ssbb/PseudoMakeMeKeyCapProfiles/stl/single_keys/cs_r2_lateral_r.stl

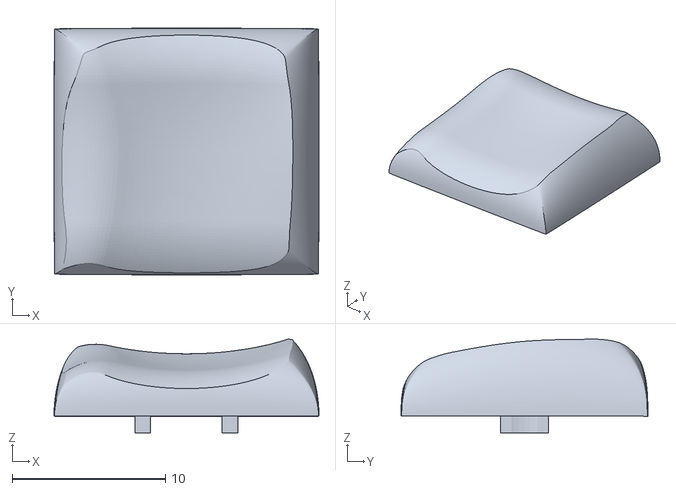
[picture p18: CAD file, 2023-09-04]
stl/single_keys/cs_r2_lateral_r.stl
17.3 x 16.1 x 6.12
