ssbb/PseudoMakeMeKeyCapProfiles/stl/single_keys/cs_r3_2.stl

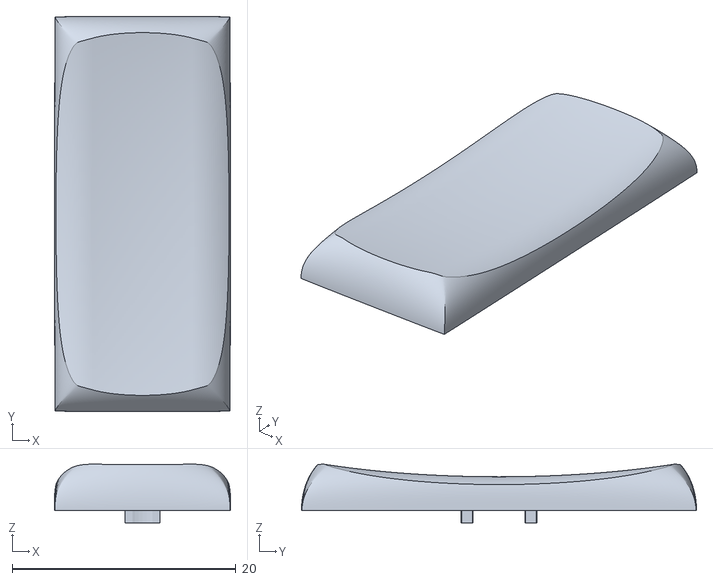
[picture p19: CAD file, 2023-09-04]
stl/single_keys/cs_r3_2.stl
15.7 x 35.3 x 5.24
