ssbb/PseudoMakeMeKeyCapProfiles/stl/single_keys/cs_r3_175.stl

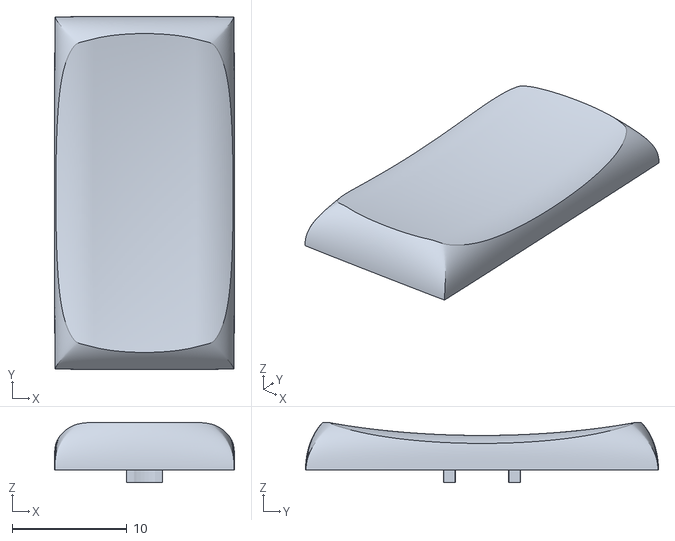
[picture p20: CAD file, 2023-09-04]
stl/single_keys/cs_r3_175.stl
15.7 x 30.8 x 5.25
