ssbb/PseudoMakeMeKeyCapProfiles/stl/single_keys/cs_r4x_1.stl

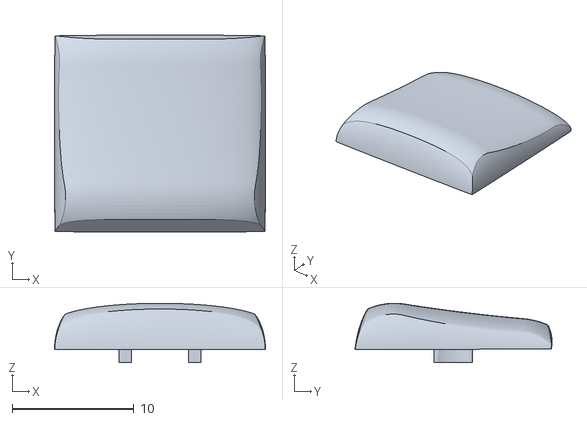
[picture p21: CAD file, 2023-09-04]
stl/single_keys/cs_r4x_1.stl
17.3 x 16.2 x 4.88
