ssbb/PseudoMakeMeKeyCapProfiles/stl/single_keys/cs_r3_125_bar.stl

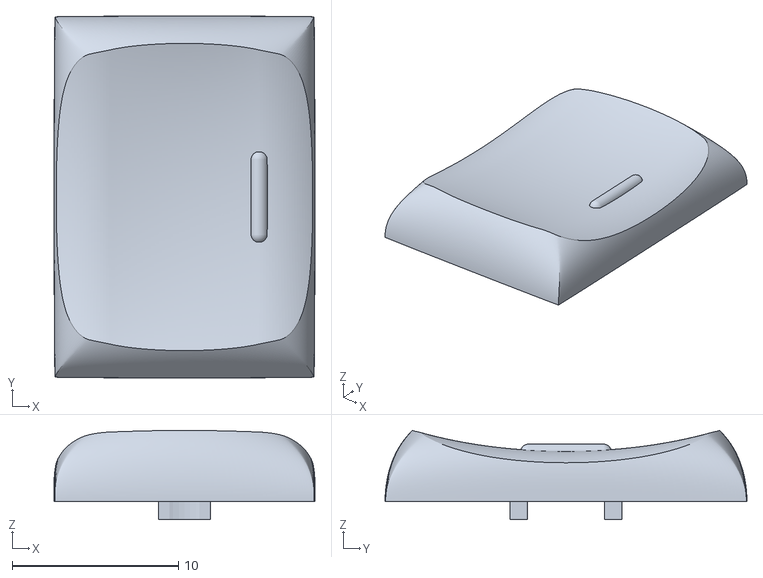
[picture p22: CAD file, 2023-09-04]
stl/single_keys/cs_r3_125_bar.stl
15.7 x 21.8 x 5.37
