ssbb/PseudoMakeMeKeyCapProfiles/stl/single_keys/cs_r3_225.stl

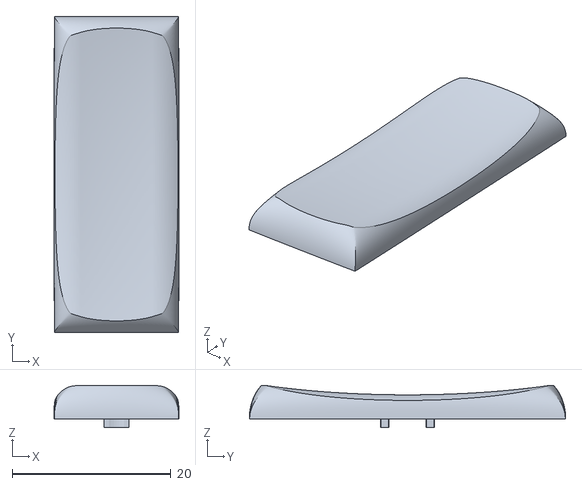
[picture p23: CAD file, 2023-09-04]
stl/single_keys/cs_r3_225.stl
15.7 x 39.8 x 5.30
