ssbb/PseudoMakeMeKeyCapProfiles/stl/single_keys/cs_r3x_1.stl

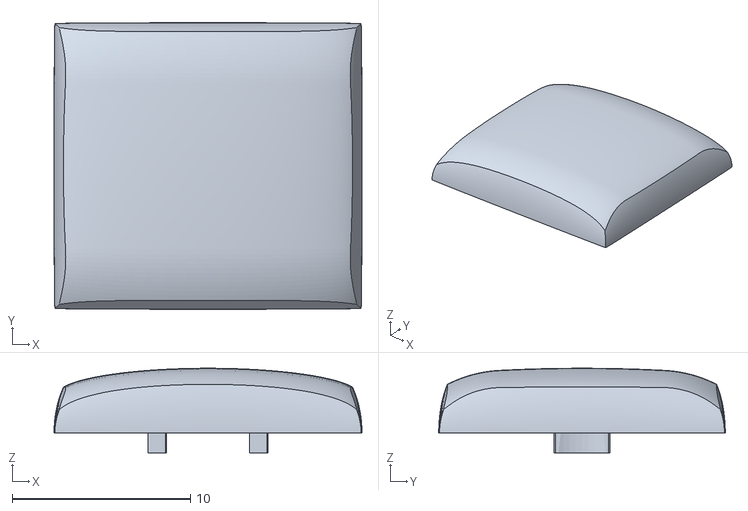
[picture p24: CAD file, 2023-09-04]
stl/single_keys/cs_r3x_1.stl
17.3 x 16.1 x 4.75
