ssbb/PseudoMakeMeKeyCapProfiles/export_cs_row_r3_homing_only.scad

use <gen_sprued_keycaps.scad>

keycap_ids = [
    "cs_r3_1_dot",
    "cs_r3_1_dot",
    "cs_r3_1_bar",
    "cs_r3_1_bar",
];

gen_sprued_keycaps(keycap_ids);
