ssbb/PseudoMakeMeKeyCapProfiles/export_cs_row_r3_homerow_bar.scad

use <gen_sprued_keycaps.scad>

keycap_ids = [
    // Left Keyboard Side
    "cs_r3_1" ,
    "cs_r3_1",
    "cs_r3_1",
    "cs_r3_1_bar",
    "cs_r3_1",

    // Right Keyboard Side
    "cs_r3_1",
    "cs_r3_1_bar",
    "cs_r3_1",
    "cs_r3_1",
    "cs_r3_1",
];

gen_sprued_keycaps(keycap_ids);
