ssbb/PseudoMakeMeKeyCapProfiles/export_cs_row_r3_regular.scad

// Use this for the top alpha row if you have a num row

use <gen_sprued_keycaps.scad>

keycap_ids = [
    // Left Keyboard Side
    "cs_r3_1",
    "cs_r3_1",
    "cs_r3_1",
    "cs_r3_1",
    "cs_r3_1",

    // Right Keyboard Side
    "cs_r3_1",
    "cs_r3_1",
    "cs_r3_1",
    "cs_r3_1",
    "cs_r3_1",
];

gen_sprued_keycaps(keycap_ids);
